drakumus/Skylight/case/IMG_1691.jpg

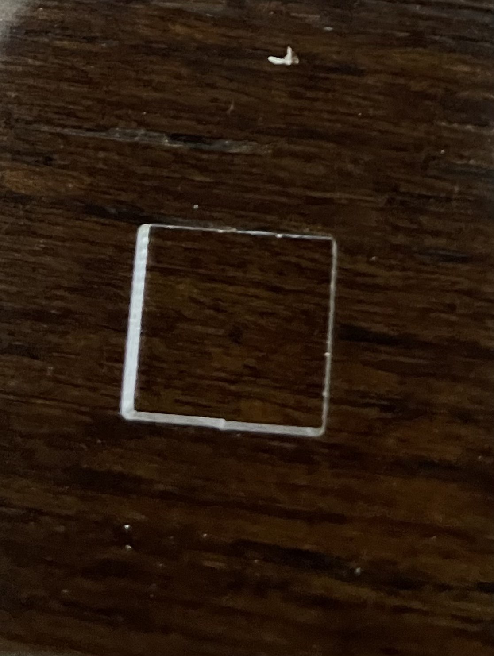
case/IMG_1691.jpg
